kalabashlabs/Midi-Planter/mp14_docs/docs/3d_components/shell.md

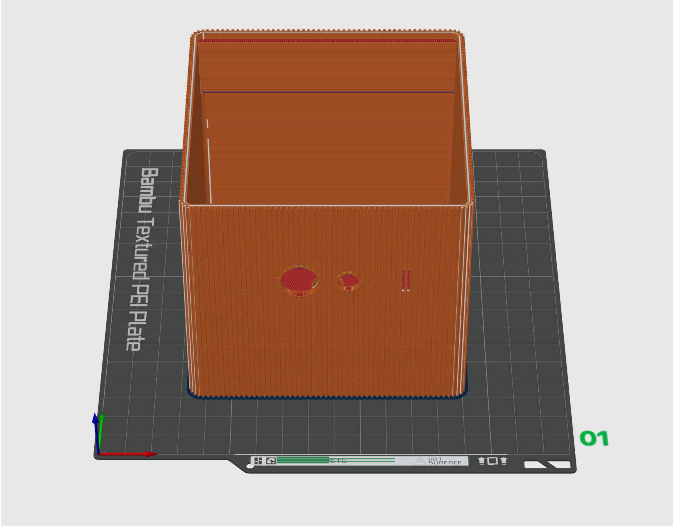
[picture p24: mp14_docs/docs/3d_components/images/shell.png]


PRINT SETTINGS:

- Material: PLA
- Layer Height: 0.3 mm
- Sparse Infill Density: 30%
- Support: Yes
